Ajakovski/Chess-Master-Board/Pictures/3D Chess Board colored.png

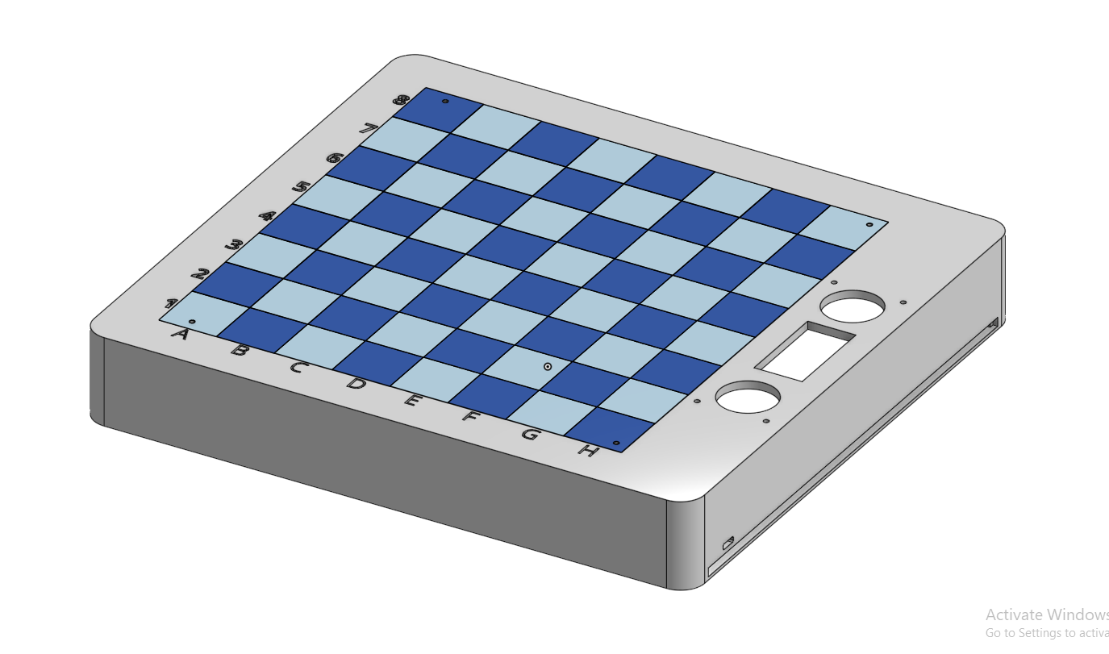
Pictures/3D Chess Board colored.png
