Ajakovski/Chess-Master-Board/Pictures/Code.png

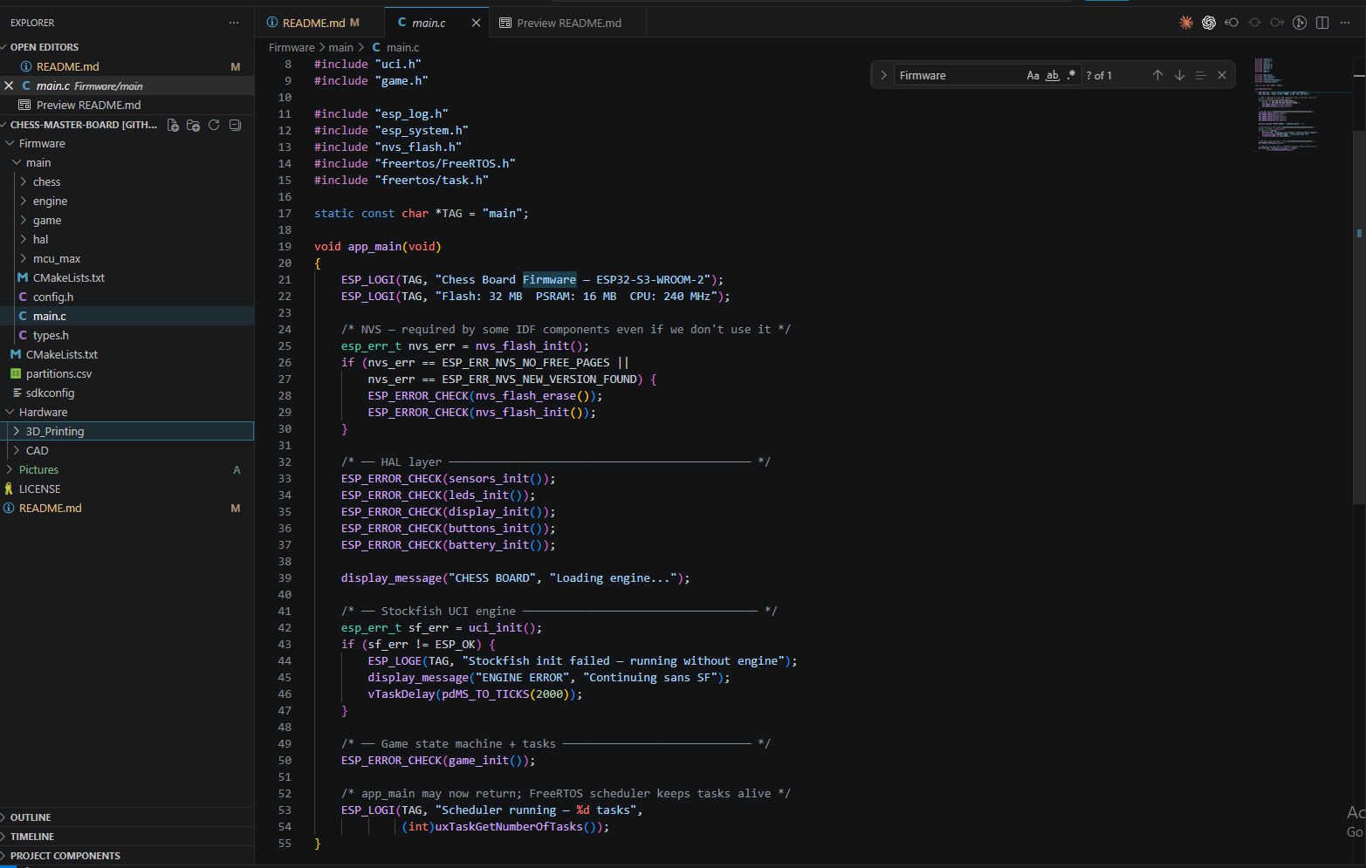
Pictures/Code.png
