Ajakovski/Chess-Master-Board/Pictures/STL_Chess_Board-removebg-preview.png

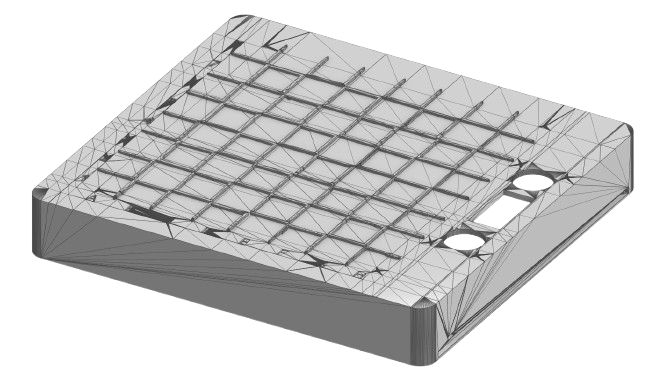
Pictures/STL_Chess_Board-removebg-preview.png
